iowlabs/TDAB/doc/PCB.png

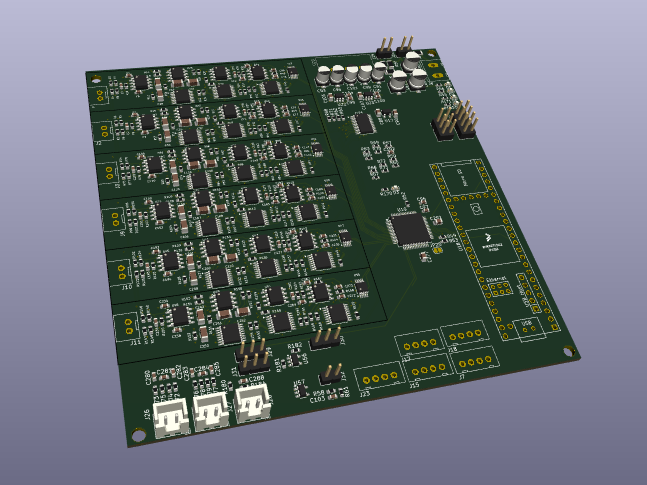
doc/PCB.png
