iowlabs/TDAB/electronics/EEG_board/EEG_board/output_files/EEG_board-removebg-preview.png

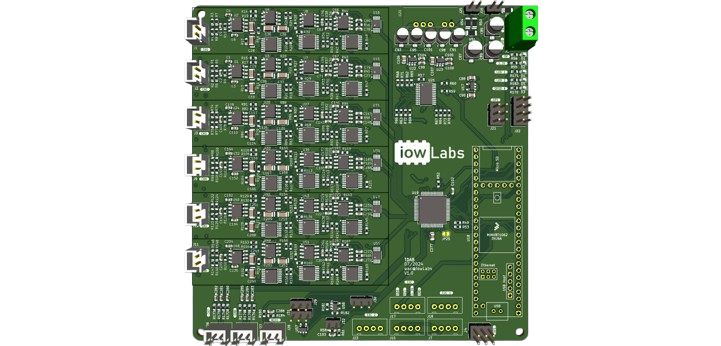
electronics/EEG_board/EEG_board/output_files/EEG_board-removebg-preview.png
