iowlabs/TDAB/electronics/EEG_board/EEG_board/output_files/EEG_board_bot-removebg-preview.png

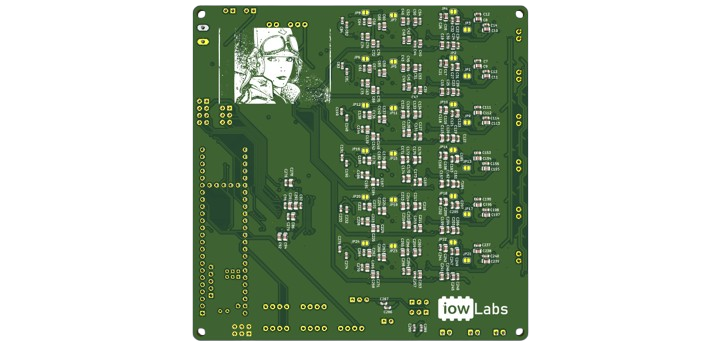
electronics/EEG_board/EEG_board/output_files/EEG_board_bot-removebg-preview.png
