iowlabs/TDAB/electronics/simulations/img/fpa.png

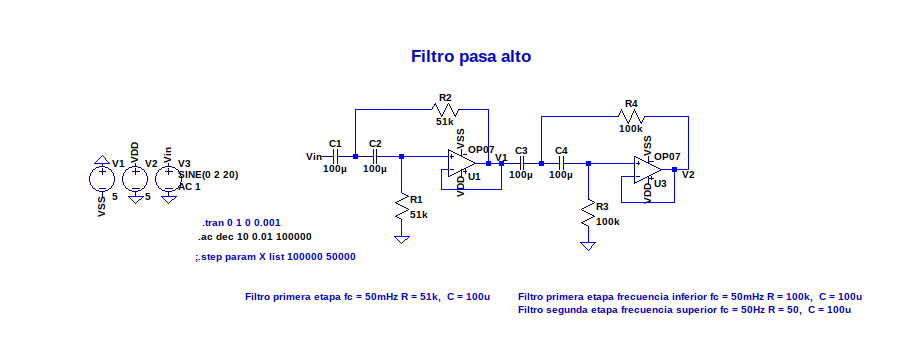
electronics/simulations/img/fpa.png
