iowlabs/TDAB/electronics/simulations/img/fpa_segunda_etapa_50mHz.png

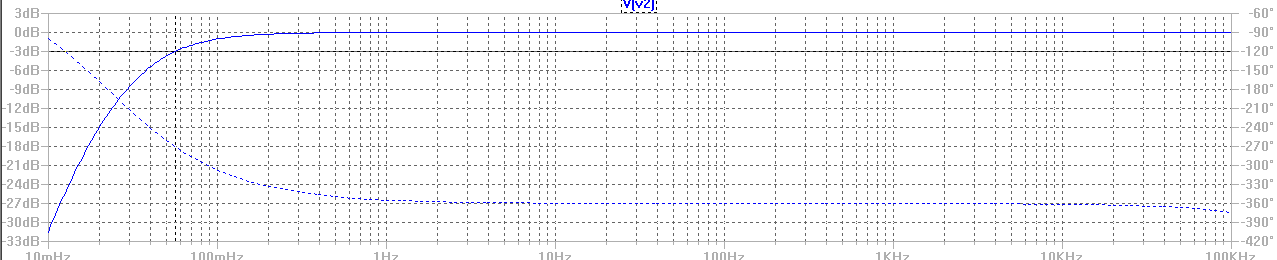
electronics/simulations/img/fpa_segunda_etapa_50mHz.png
