iowlabs/TDAB/electronics/simulations/img/fpb_primera_etapa_10k.png

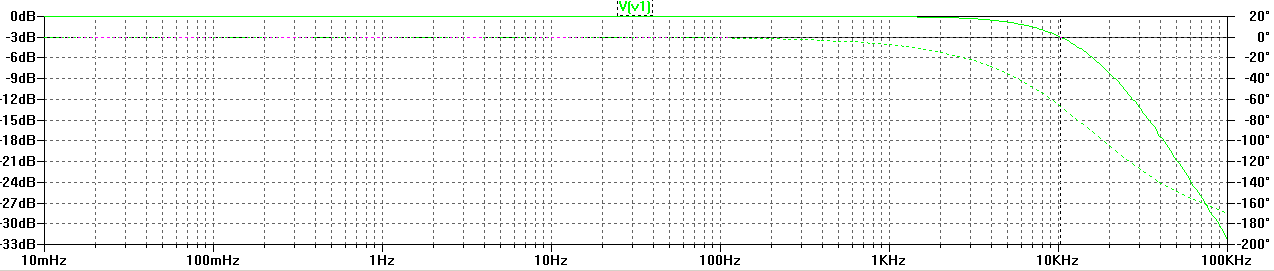
electronics/simulations/img/fpb_primera_etapa_10k.png
