iowlabs/TDAB/electronics/simulations/img/fpb_segunda_etapa_superior_10k.png

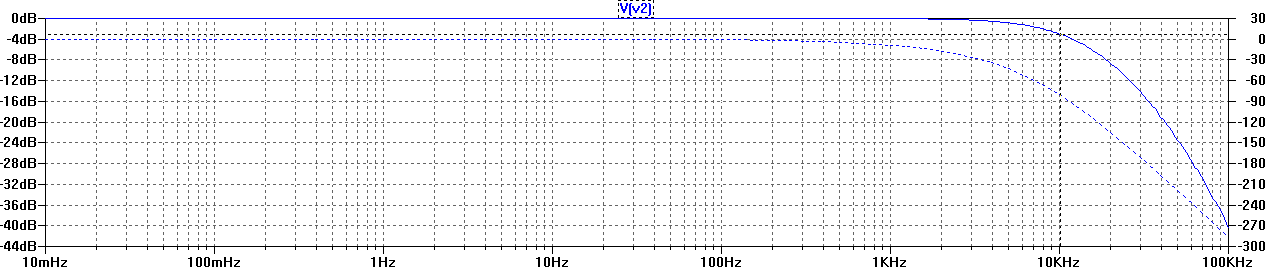
electronics/simulations/img/fpb_segunda_etapa_superior_10k.png
