iowlabs/TDAB/electronics/simulations/img/hpf_e1.png

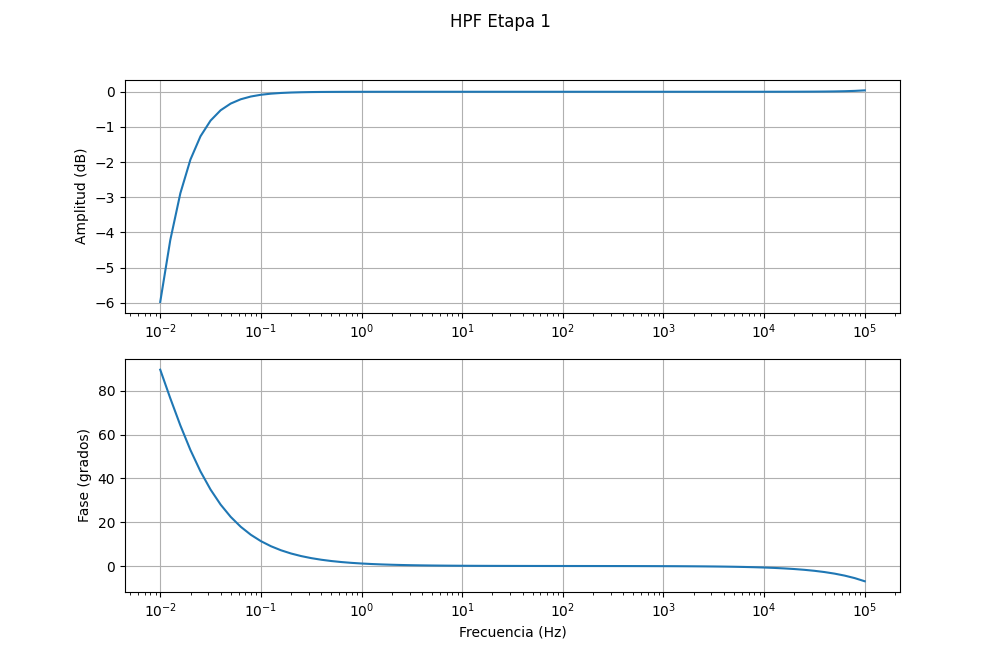
electronics/simulations/img/hpf_e1.png
