iowlabs/TDAB/electronics/simulations/img/hpf_e2_x1k.png

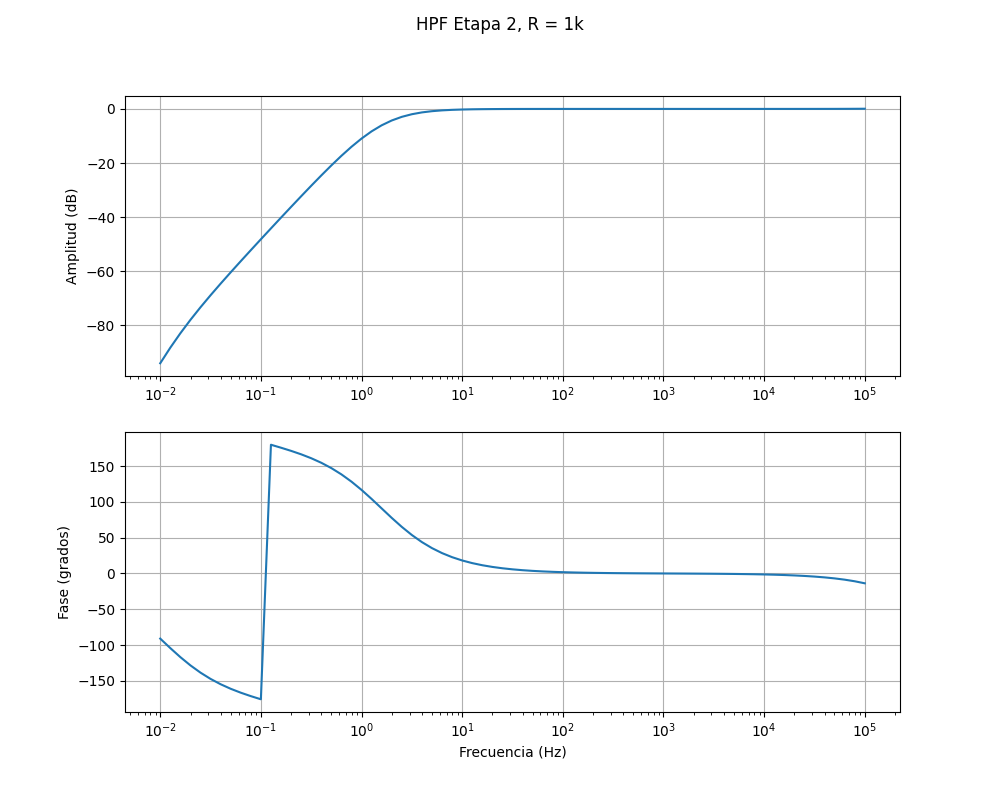
electronics/simulations/img/hpf_e2_x1k.png
