iowlabs/TDAB/electronics/simulations/img/hpf_e2_x10.png

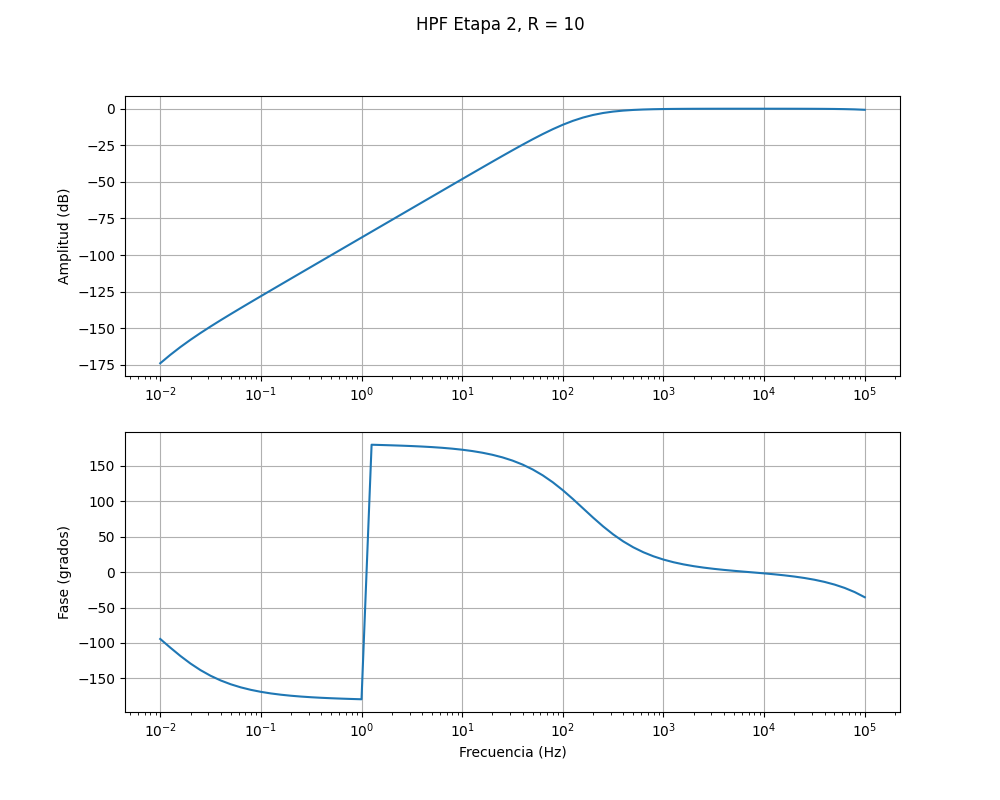
electronics/simulations/img/hpf_e2_x10.png
