iowlabs/TDAB/electronics/simulations/img/lpf_e1.png

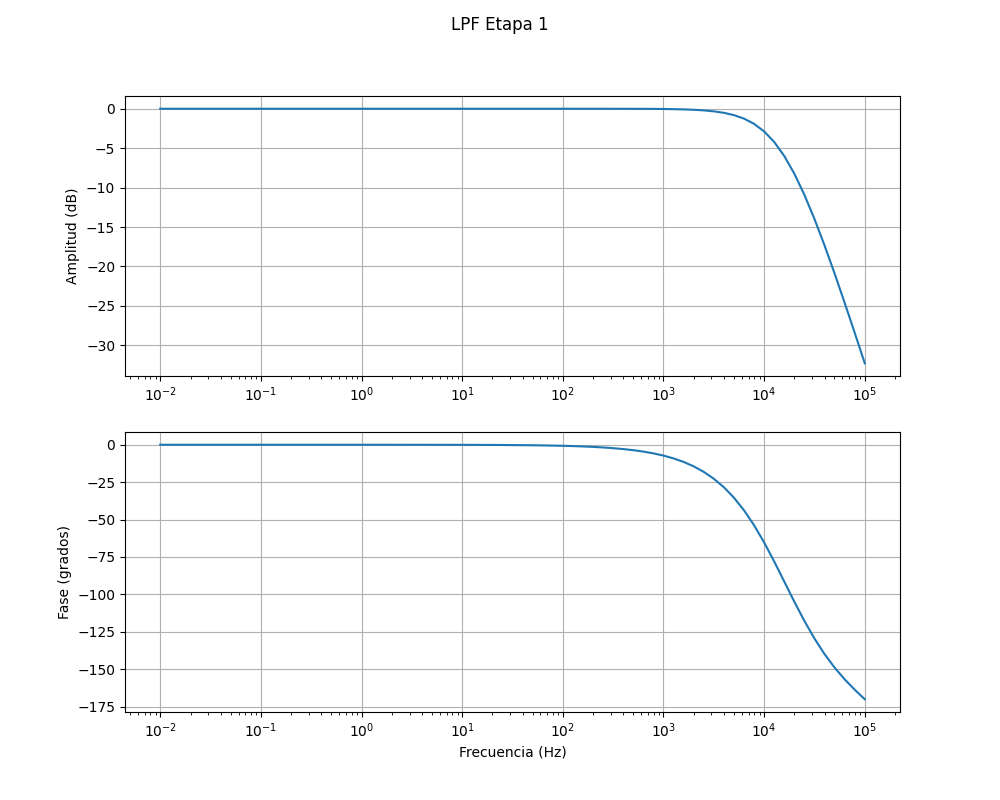
electronics/simulations/img/lpf_e1.png
