iowlabs/TDAB/electronics/simulations/img/lpf_e2_x1k.png

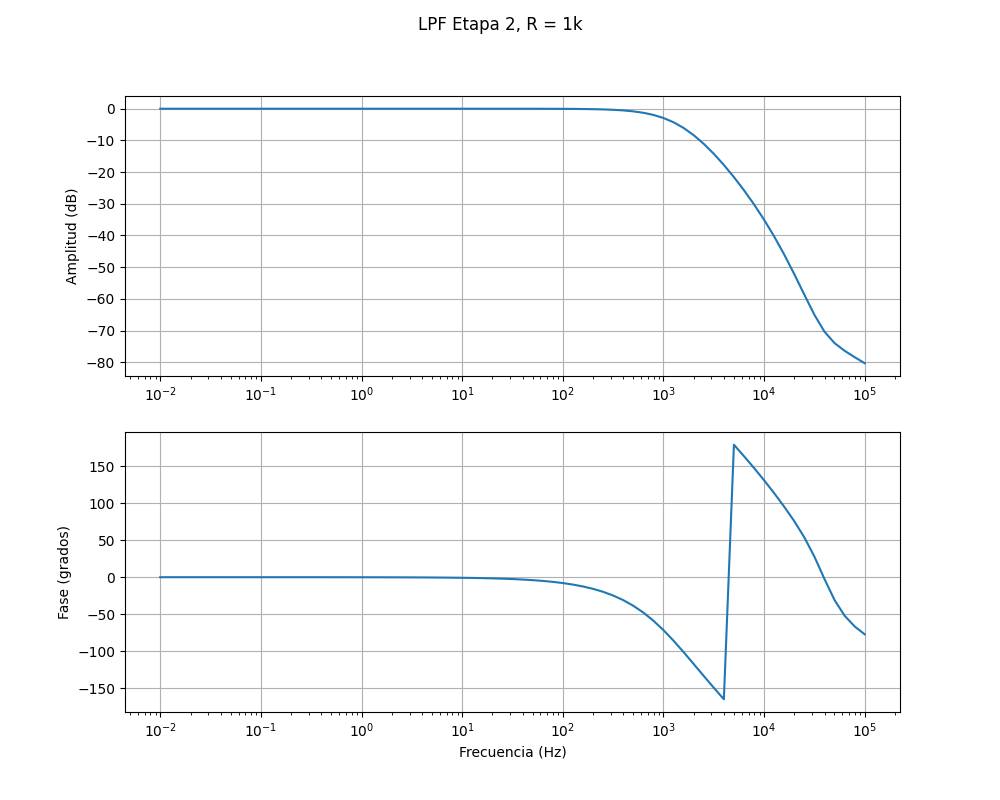
electronics/simulations/img/lpf_e2_x1k.png
