iowlabs/TDAB/electronics/simulations/img/lpf_e2_x10.png

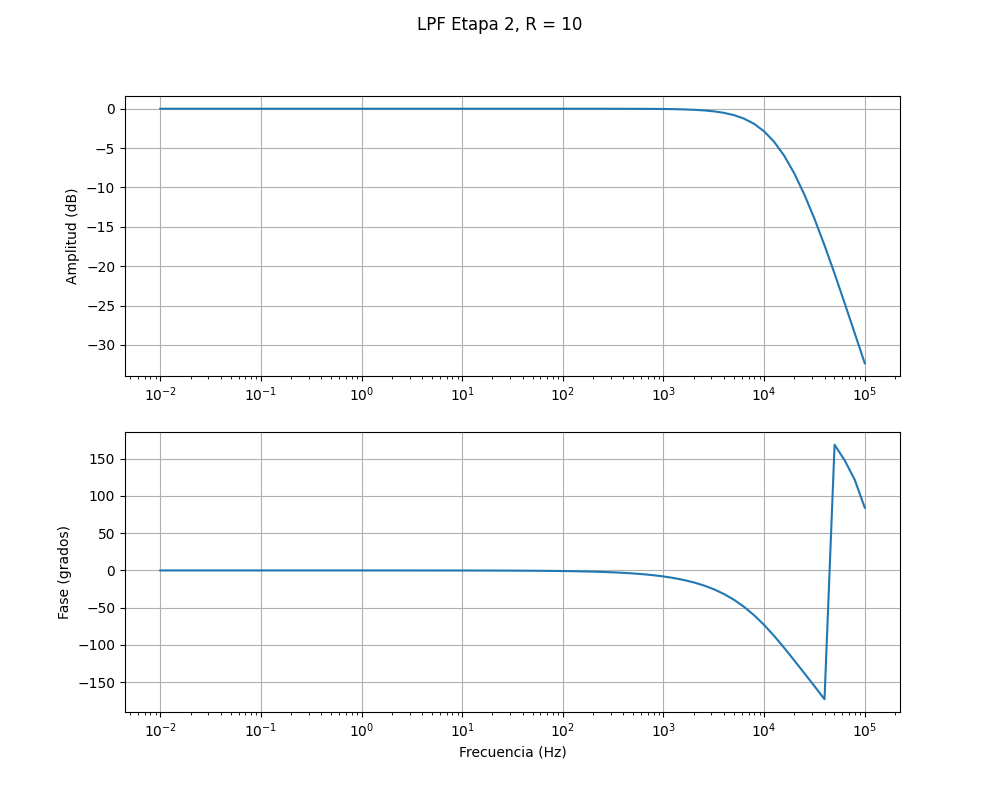
electronics/simulations/img/lpf_e2_x10.png
