iowlabs/TDAB/electronics/simulations/img/lpf_e2_x200k.png

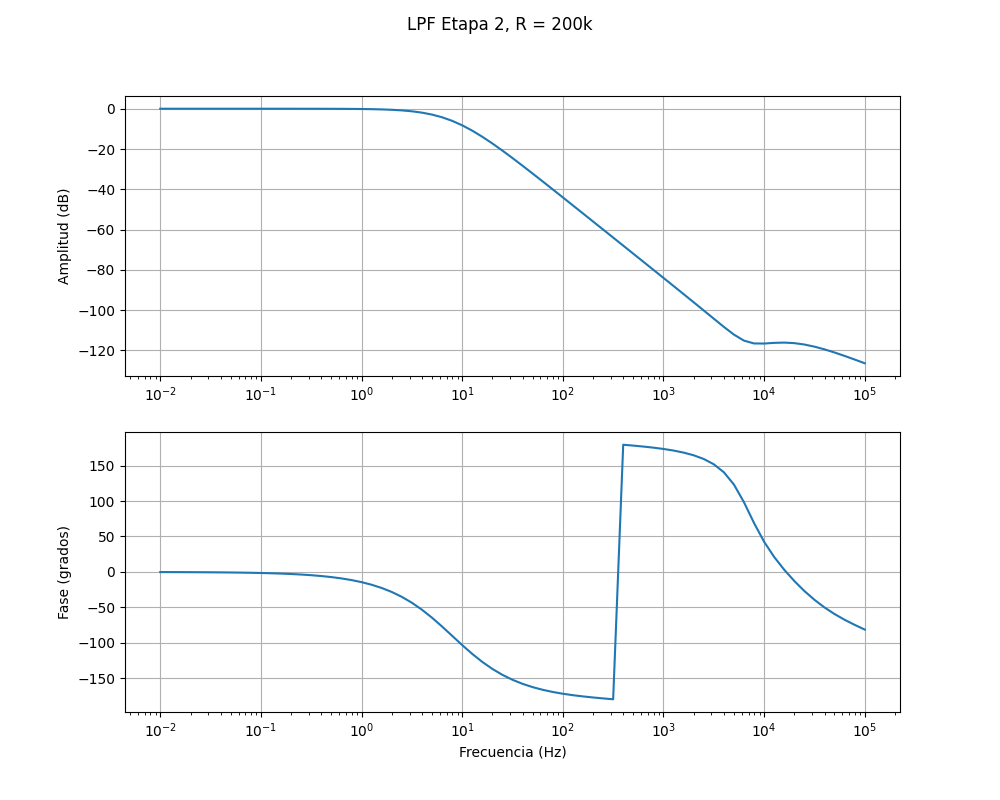
electronics/simulations/img/lpf_e2_x200k.png
