iowlabs/TDAB/electronics/simulations/EEG.asc

C1: cap; 0.01µ
C2: cap; 0.01µ
C3: cap; 1n
C4: cap; 100p
C5: cap; 100p
C6: cap; 0.1µ
R1: res; 33k
R2: res; 33k
R3: res; 17.25k
R4: res; 10
R5: res; 4.7k
R6: res; 4.7k
R7: res; 10Meg
R8: res; 10Meg
R9: res; 10K
R10: res; 1K
U1: OP07
U2: AD8475
U3: AD8421
U4: OP07
U5: OP07
V1: voltage; 12V
V2: voltage; 12V
V3: voltage; SINE(0 100u 2 0 0 -90)
V4: voltage; SINE(0 10u 1k)
V5: voltage; 1.5
V6: voltage; SINE(0 100u 2 0 0 -90)
V7: voltage; SINE(0 10u 1k)
V8: voltage; 40m
Named nets: 0, vss, Vdd, V_in+, Vss, V_in-, Vocm, Vin2
.tran 0 1 0 0.01
