iowlabs/TDAB/electronics/simulations/EEG_complete_tran.asc

C1: cap; 0.001µ
C2: cap; 0.001µ
C3: cap; 1n
C4: cap; 100p
C5: cap; 100p
C7: cap; 100µ
C8: cap; 100µ
R1: res; 10k
R2: res; 10k
R3: res; 1k
R4: res; 10
R5: res; 4.7k
R6: res; 4.7k
R7: res; 10Meg
R8: res; 10Meg
R9: res; 10K
R10: res; 1k
R11: res; 51k
R12: res; 51k
U1: OP07
U2: AD8475
U3: AD8421
U6: OP07
U7: OP07
V1: voltage; 2.5
V2: voltage; 2.5
V3: voltage; SINE(0 25m 100 0 0 -90)
V5: voltage; 0
V6: voltage; SINE(0 25m 100 0 0 -90)
V8: voltage; 40m
Named nets: 0, vss, Vdd, V_in+, Vss, V_in-, Vocm, Vin2
.tran 0 0.5 0 0.01
Frecuencia de corte inferior 0.05
Para señales de micro usar R4 10
Para señales de milis usar R4 1.1K
Frecuencia de corte superior 10k
