iowlabs/TDAB/electronics/simulations/hpf.asc

C1: cap; 100µ
C2: cap; 100µ
C3: cap; 100µ
C4: cap; 100µ
R1: res; 51k
R2: res; 51k
R3: res; 100k
R4: res; 100k
U1: OP07
U3: OP07
V1: voltage; 5
V2: voltage; 5
V3: voltage; SINE(0 2 20); AC 1
Named nets: 0, VDD, VSS, Vin, V2, V1
;.step param X list 100000 50000
.ac dec 10 0.01 100000
.tran 0 1 0 0.001
Filtro pasa alto
Filtro primera etapa fc = 50mHz R = 51k,  C = 100u
Filtro primera etapa frecuencia inferior fc = 50mHz R = 100k,  C = 100u
Filtro segunda etapa frecuencia superior fc = 50Hz R = 50,  C = 100u
