iowlabs/TDAB/electronics/simulations/lpf.asc

C1: cap; 0.001µ
C2: cap; 0.001µ
C3: cap; 0.01µ
C4: cap; 0.01µ
R1: res; 10k
R2: res; 10k
R3: res; 200
R4: res; 200
U1: OP07
U3: OP07
V1: voltage; 12
V2: voltage; 12
V3: voltage; ""; AC 1
Named nets: 0, VDD, VSS, Vin, V2, V1
.ac dec 10 0.01 100000
.step param X list 100 1000 10000 100000
frecuencia inferior 10KHz    R 10k  C 0.001u
frecuencia superior 10kHz    R 200  C 0.01u
frecuencia inferior 100Hz    R 100k C 0.01u
Filtro pasa bajos
