iowlabs/TDAB/electronics/simulations/pb.asc

C1: cap; 0.001µ
C2: cap; 0.001µ
C3: cap; 0.01µ
C4: cap; 0.01µ
C5: cap; 100µ
C6: cap; 100µ
C7: cap; 100µ
C8: cap; 100µ
R1: res; 10k
R2: res; 10k
R3: res; 10k
R4: res; 10k
R5: res; 51k
R6: res; 51k
R7: res; {X}
R8: res; {X}
R9: res; 2k
R10: res; 200k
U1: OP07
U2: OP07
U3: OP07
U4: OP07
U5: OP07
V1: voltage; 12
V2: voltage; 12
V3: voltage; ""; AC 1
Named nets: 0, VDD, VSS, Vin, V2, V1, v3, V4, V5
.ac dec 10 0.01 100000
.step param X list  100000 100 10
Frecuencia de corte inferior 0.05  ---> 100u - 51k
Frecuencia de corte superior 250  ---> 100u - 10
Frecuencia de corte inferior 0.056 ---> 100u - 100k
Filtro pasa Altos
Filtro pasa bajos
Frecuencia de corte superior 10k ---> 100u - 51k
Frecuencia de corte superior 250  ---> 100u - 10
Frecuencia de corte inferior 0.056 ---> 100u - 100k
