iowlabs/TDAB/electronics/simulations/Rechaza banda pasivo R-C.asc

C1: cap; 5µ
C2: cap; 5µ
C3: cap; 10µ
R1: res; 636
R2: res; 636
R3: res; 318
V1: voltage; ""; AC 1
Named nets: 0, Vout
.ac dec 50 0.01 100000
